JuliaArellano/Trabajo_Fin_Grado_GIS/Documentación del proyecto/Diagramas/caso_uso_flujo.png

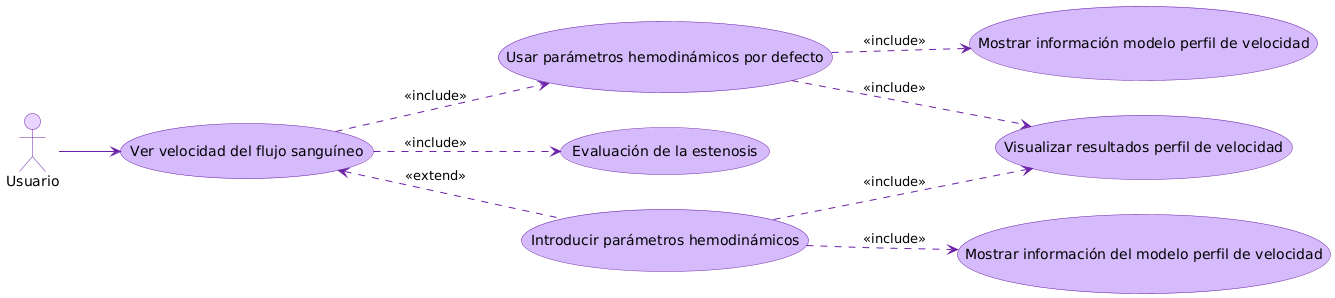
Documentación del proyecto/Diagramas/caso_uso_flujo.png
